fhirschmann/fumex/docs/audit-2026-09-23/front_joint.png

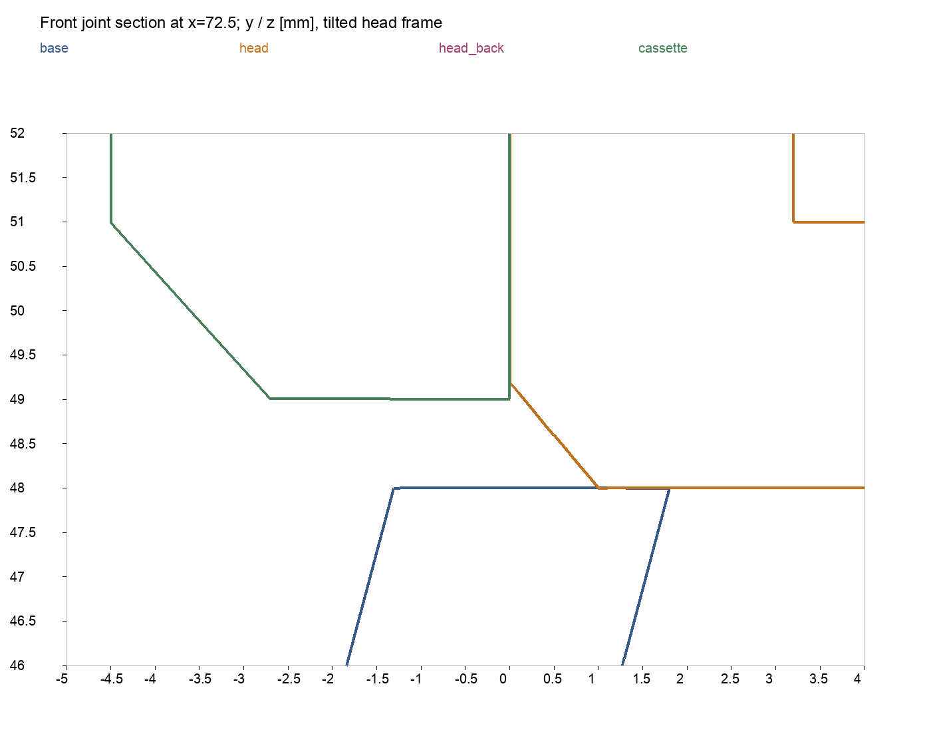
docs/audit-2026-09-23/front_joint.png
