fhirschmann/fumex/docs/preprint-audit-2026-09-25/rear-top-corner.png

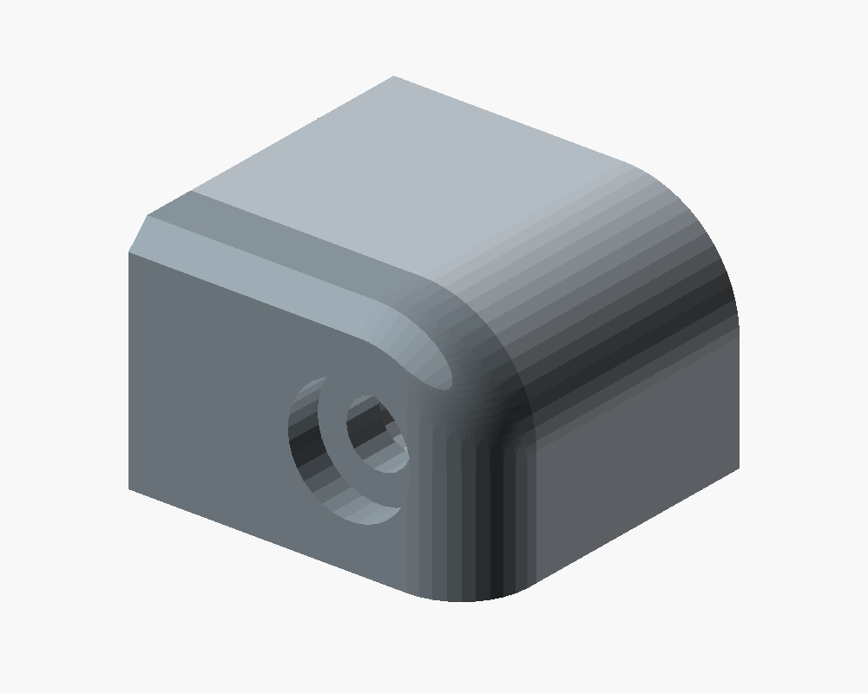
docs/preprint-audit-2026-09-25/rear-top-corner.png
