fhirschmann/fumex/stl/foot.stl

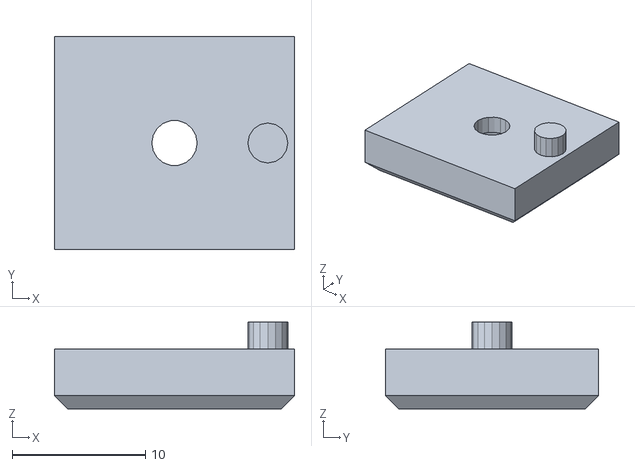
[picture p46: CAD file, 2026-09-26]
stl/foot.stl
18.0 x 16.0 x 6.50
